Shane-Wood-TL/SW-Quadruped/01_CAD/V10/Hip/CAN_SERVO_PCB_HOLDER.FCStd

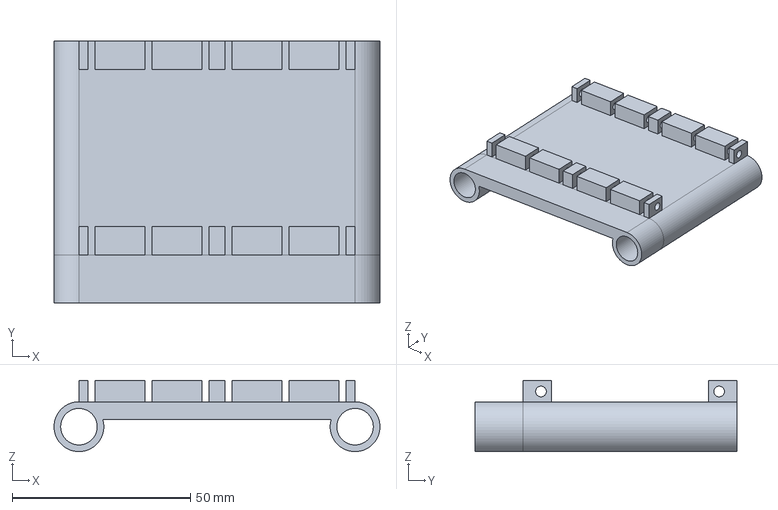
[picture p15: CAD file, 2025-10-24]
01_CAD/V10/Hip/CAN_SERVO_PCB_HOLDER.FCStd
91.5 x 73.5 x 20.0 mm
