Shane-Wood-TL/SW-Quadruped/01_CAD/V10/Non_Printed_parts/MG996R.FCStd

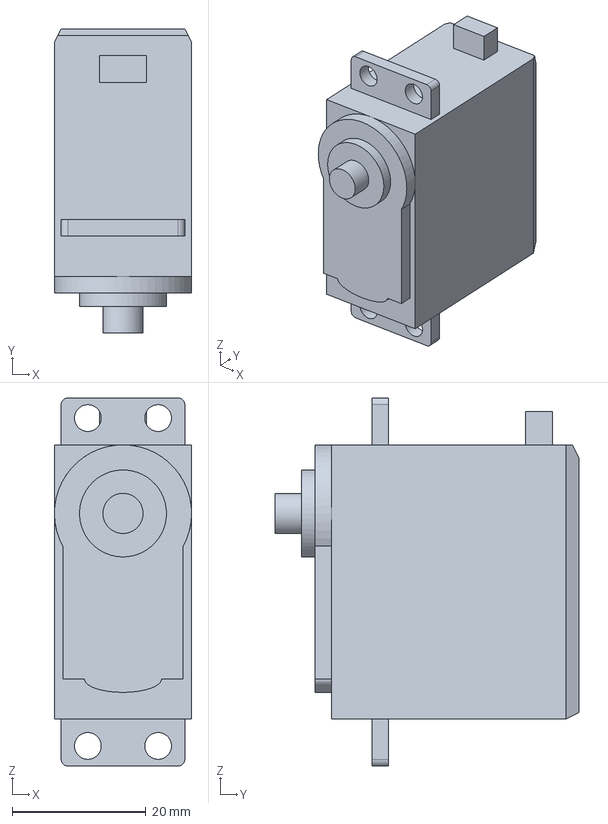
[picture p16: CAD file, 2025-10-24]
01_CAD/V10/Non_Printed_parts/MG996R.FCStd
20.5 x 45.5 x 55.0 mm
