Shane-Wood-TL/SW-Quadruped/01_CAD/V10/Upper_Leg/UPPER_LEG_OUTER.FCStd

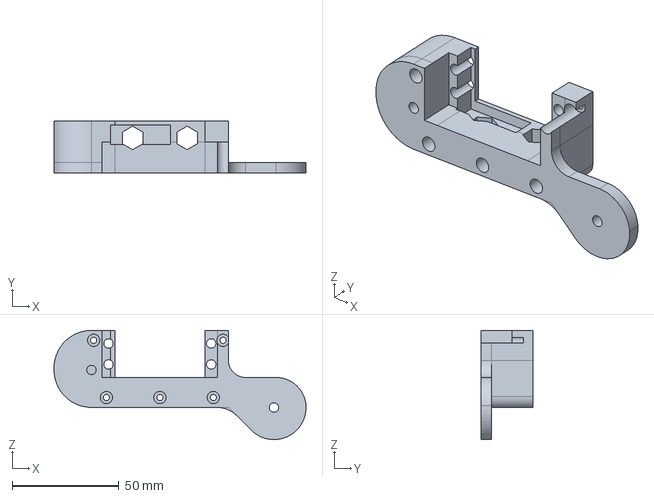
[picture p17: CAD file, 2025-10-24]
01_CAD/V10/Upper_Leg/UPPER_LEG_OUTER.FCStd
117.8 x 24.5 x 51.0 mm
