Shane-Wood-TL/SW-Quadruped/CAD/V5/Body/bno055cover.FCStd

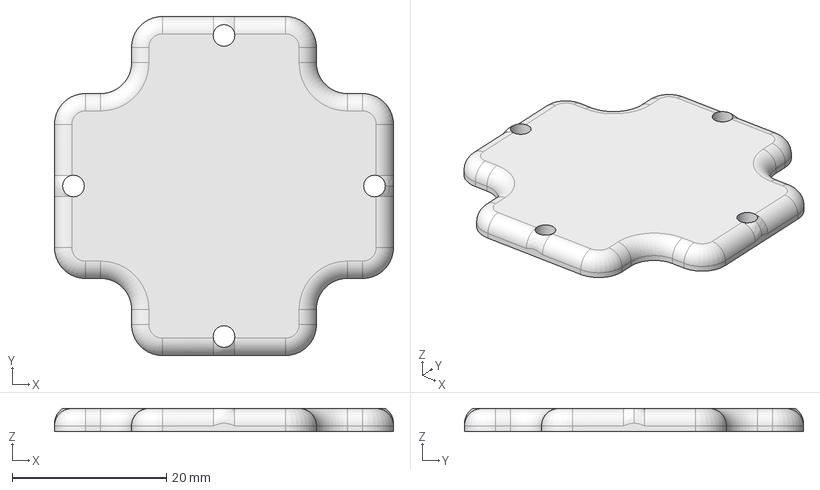
[picture p18: CAD file, 2023-03-16]
CAD/V5/Body/bno055cover.FCStd
44.0 x 44.0 x 3.00 mm
