Shane-Wood-TL/SW-Quadruped/CAD/V5/Hip/backhipplate.FCStd

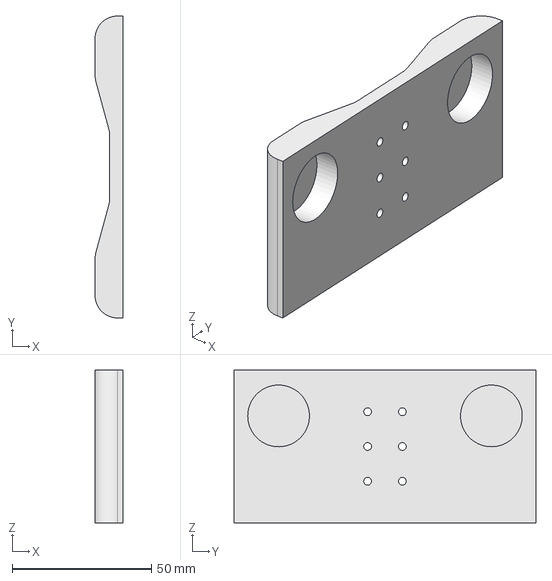
[picture p19: CAD file, 2023-02-27]
CAD/V5/Hip/backhipplate.FCStd
10.0 x 108.5 x 55.0 mm
