Shane-Wood-TL/SW-Quadruped/CAD/V5/NonPrintedParts/6servohorn.FCStd

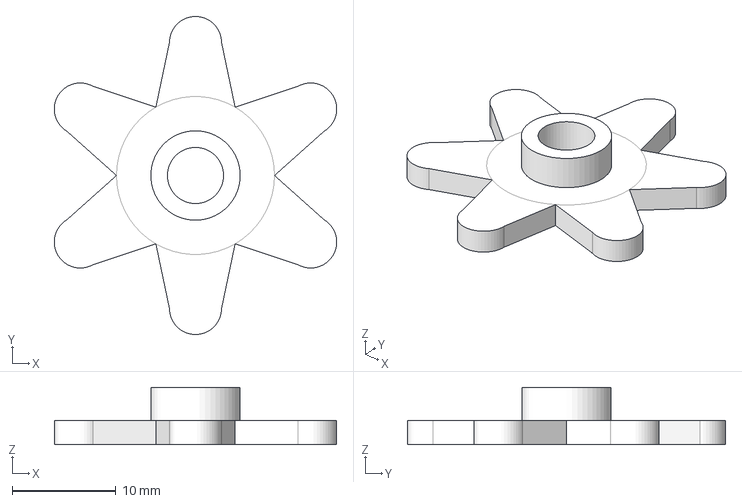
[picture p20: CAD file, 2023-02-27]
CAD/V5/NonPrintedParts/6servohorn.FCStd
27.2 x 30.6 x 5.50 mm
