Shane-Wood-TL/SW-Quadruped/CAD/V5/Upper_leg/outerUpperLeg.FCStd

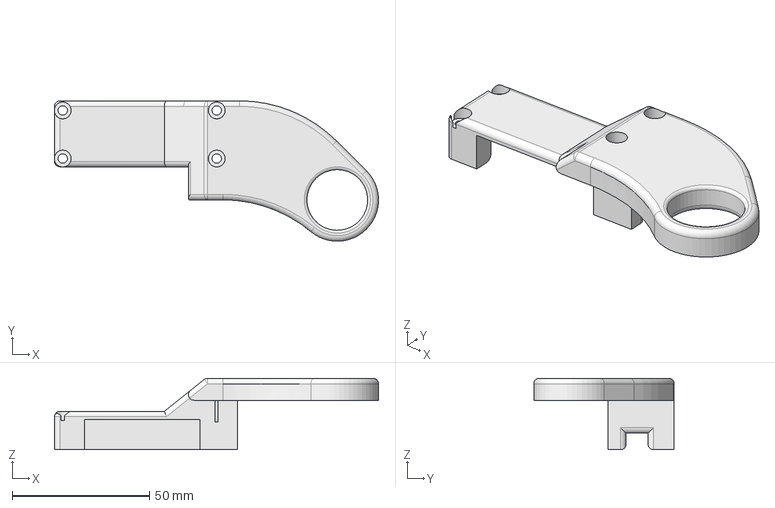
[picture p21: CAD file, 2023-02-27]
CAD/V5/Upper_leg/outerUpperLeg.FCStd
117.8 x 51.1 x 26.0 mm
