Shane-Wood-TL/SW-Quadruped/01_CAD/V10/Hip/OUTER_PLATE.FCStd

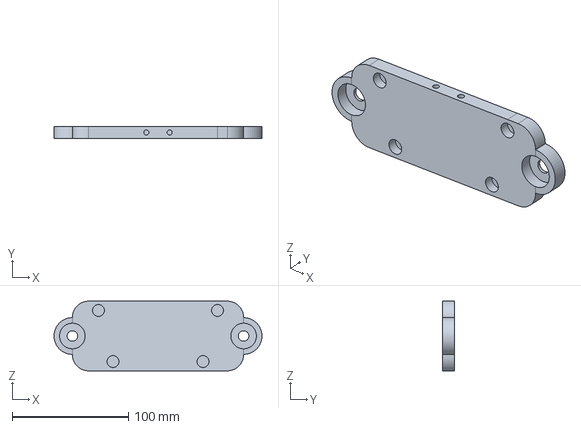
[picture p22: CAD file, 2025-10-24]
01_CAD/V10/Hip/OUTER_PLATE.FCStd
179.1 x 10.0 x 60.0 mm
