Shane-Wood-TL/SW-Quadruped/01_CAD/V10/Non_Printed_parts/circularServoHorn.FCStd

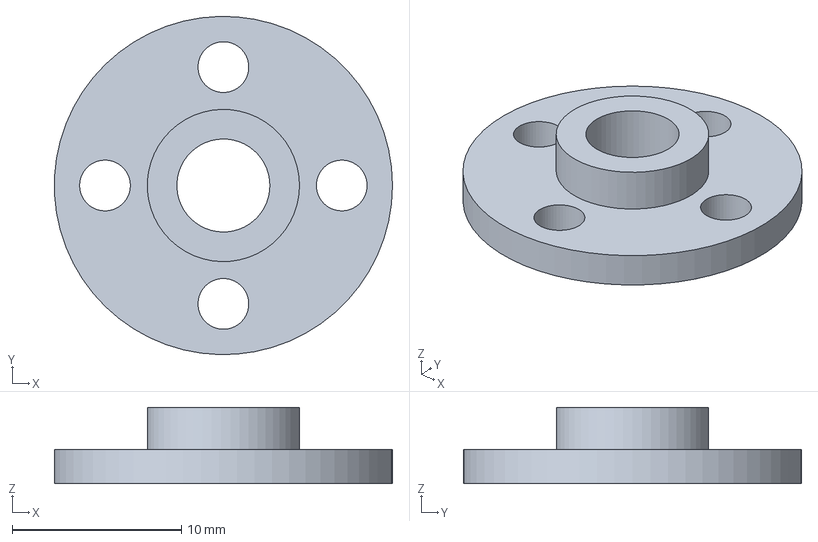
[picture p23: CAD file, 2025-10-24]
01_CAD/V10/Non_Printed_parts/circularServoHorn.FCStd
20.0 x 20.0 x 4.50 mm
