Shane-Wood-TL/SW-Quadruped/CAD/V5/Body/topBody.FCStd

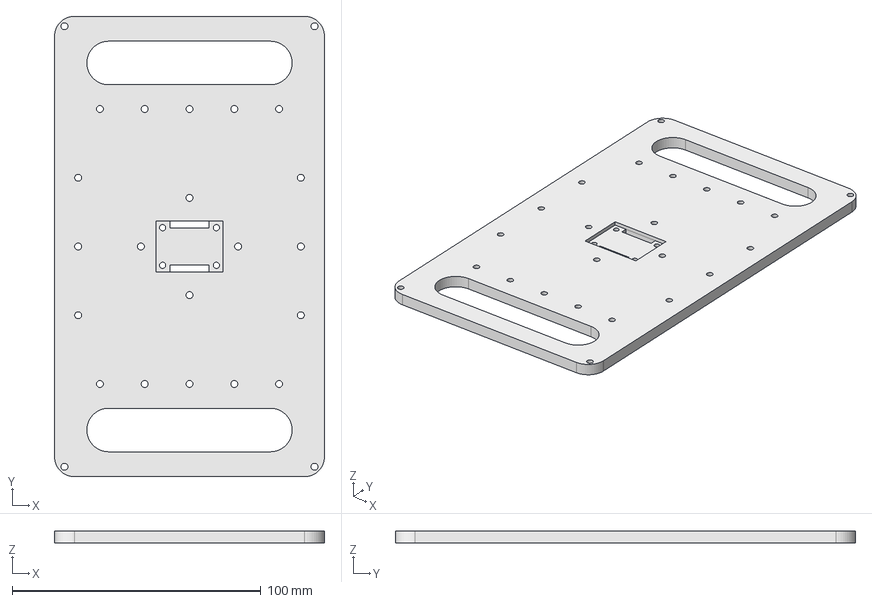
[picture p24: CAD file, 2023-02-27]
CAD/V5/Body/topBody.FCStd
108.5 x 185.0 x 5.00 mm
