Shane-Wood-TL/SW-Quadruped/CAD/V5/Hip/hipMotorHolder.FCStd

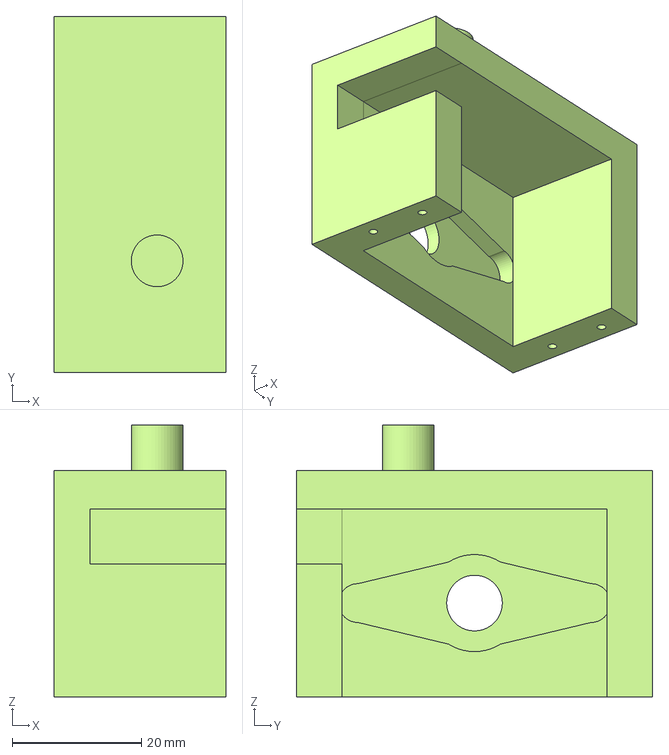
[picture p25: CAD file, 2023-02-27]
CAD/V5/Hip/hipMotorHolder.FCStd
26.5 x 55.0 x 42.0 mm
