Shane-Wood-TL/SW-Quadruped/CAD/V5/NonPrintedParts/608Zballbearing.FCStd

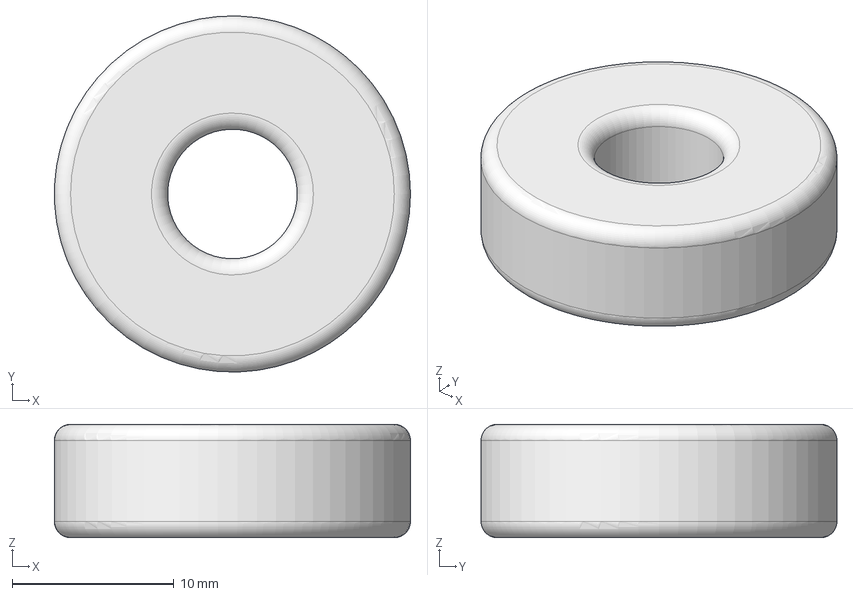
[picture p26: CAD file, 2023-02-27]
CAD/V5/NonPrintedParts/608Zballbearing.FCStd
22.0 x 22.0 x 7.00 mm
