Shane-Wood-TL/SW-Quadruped/01_CAD/V10/Hip/KNEE_MOTOR_HOLDER.FCStd

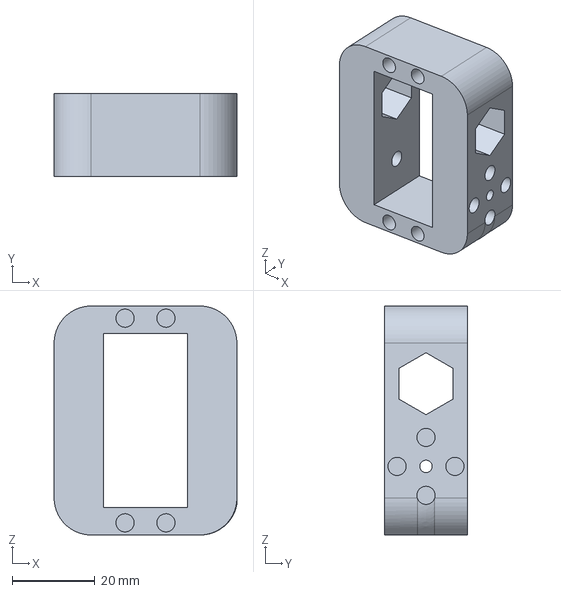
[picture p27: CAD file, 2025-10-24]
01_CAD/V10/Hip/KNEE_MOTOR_HOLDER.FCStd
44.3 x 20.0 x 55.4 mm
