Shane-Wood-TL/SW-Quadruped/CAD/V5/Body/body.FCStd

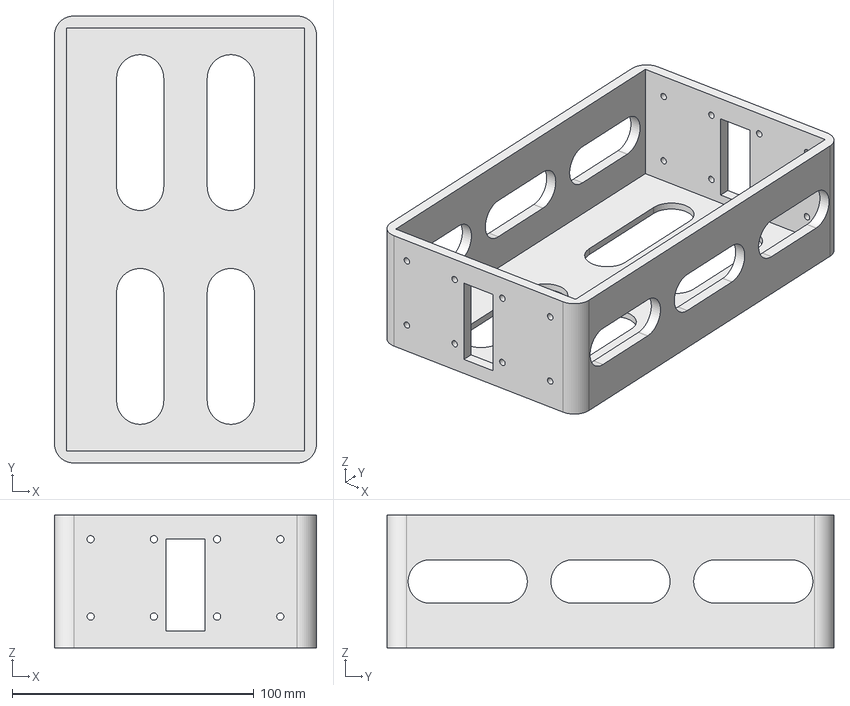
[picture p28: CAD file, 2023-02-27]
CAD/V5/Body/body.FCStd
108.5 x 185.0 x 55.0 mm
