Shane-Wood-TL/SW-Quadruped/CAD/V5/NonPrintedParts/4servohorn.FCStd

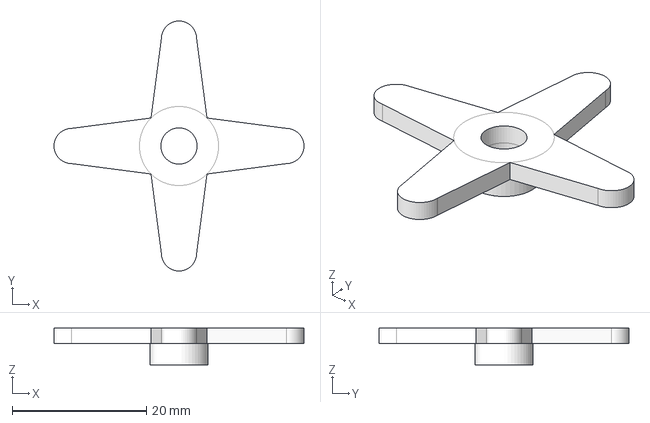
[picture p29: CAD file, 2023-02-27]
CAD/V5/NonPrintedParts/4servohorn.FCStd
37.3 x 37.2 x 5.50 mm
