Shane-Wood-TL/SW-Quadruped/02_Code/ESP-IDF/QuadrupedRobot/include/hardware_setup/robot_constants.h

#ifndef __robot_constants__
#define __robot_constants__
//dimensions of the bot
#define BODY_LENGTH 480.0f
#define BODY_WIDTH 150.0f

#define A_LENGTH_V 95.0f
#define B_LENGTH_V 95.0f
#define H_LENGTH_V 110.0f


#define aHip 3  //
#define aKnee 4  //
#define aAnkle 5 //

#define bHip 2 //
#define bKnee 1  //
#define bAnkle 0 //

#define cHip 2   //
#define cKnee 1  //
#define cAnkle 0 //

#define dHip 3    //
#define dKnee 4  //
#define dAnkle 5 //

#endif
