Shane-Wood-TL/SW-Quadruped/02_Code/ESP-IDF/QuadrupedRobot/include/hardware_setup/motor_offsets.h

#ifndef __motor_offsets__
#define __motor_offsets__

#define A_HIP_OFFSET -6
#define A_KNEE_OFFSET 5
#define A_ANKLE_OFFSET -23

#define B_HIP_OFFSET 3
#define B_KNEE_OFFSET 15
#define B_ANKLE_OFFSET -20

#define C_HIP_OFFSET 5
#define C_KNEE_OFFSET 5
#define C_ANKLE_OFFSET -15

#define D_HIP_OFFSET -2
#define D_KNEE_OFFSET 10
#define D_ANKLE_OFFSET -20

#endif
