Shane-Wood-TL/SW-Quadruped/02_Code/Quadruped_Robot/include/robotConstants.h

//servo motor pwm limits
#define USMIN 771  // min value given from arduino lib
#define USMAX 2193 // max value given from arduino lib

//dimensions of the bot
#define yHalfDis 122
#define zHalfDis 190
// constant distances
#define aLength 95 // upper leg length more red
#define bLength 95 // lower leg length more purple
#define Ldis 50


#define aHip 3  //
#define aKnee 4  //
#define aAnkle 5 //

#define bHip 2 //
#define bKnee 1  //
#define bAnkle 0 //

#define cHip 2   //
#define cKnee 1  //
#define cAnkle 0 //

#define dHip 3    //
#define dKnee 4  //
#define dAnkle 5 //
