Shane-Wood-TL/SW-Quadruped/02_Code/ESP-IDF/QuadrupedRobot/include/math_functions.h

#ifndef __extra_math__
#define __extra_math__
//------------------------------------------------------------------------------------------------
//Extra Math
#define PI 3.14
float radians_to_degrees(float radians);
float degrees_to_radians(float degrees);
float pythagorean_hypotenuse(float a, float b);
float pythagorean_side(float a, float c);
float law_of_cosines(float a, float b, float c);
#endif
